zbigsr814/urzadzenie_do_nauki_Brillea/zdjęcia i filmy/5.jpg

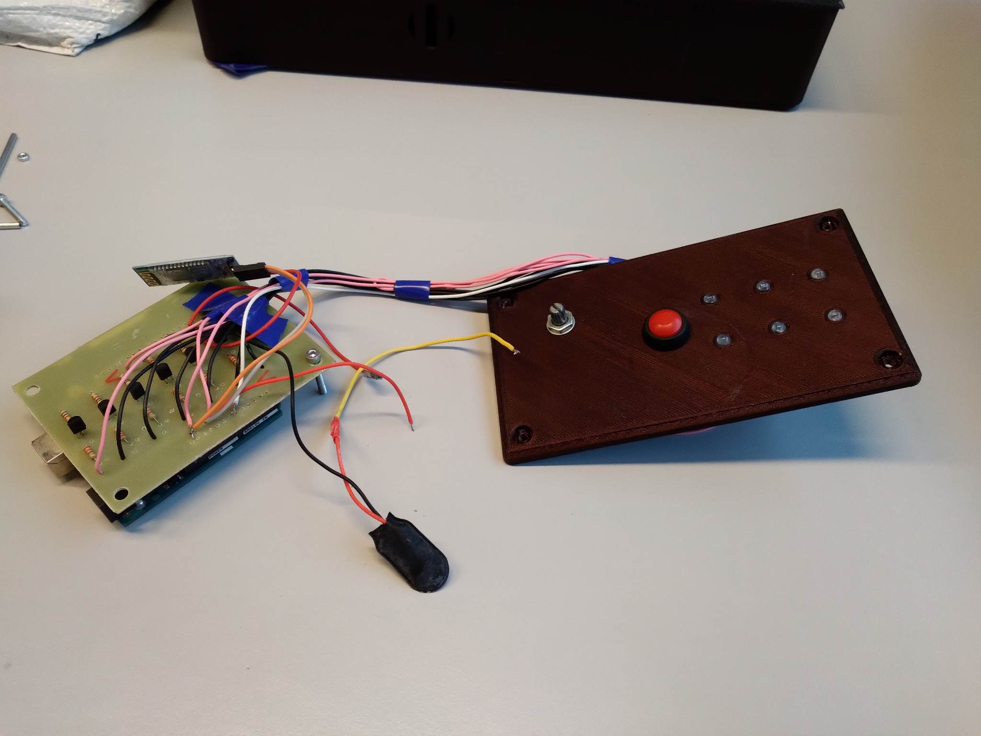
zdjęcia i filmy/5.jpg
